planmarks/2FAK/Firmware/Non-Resident CTAP2.0-2.1/targets/stm32l432/src/u2f_compat.h

#ifndef U2F_COMPAT_H
#define U2F_COMPAT_H

// FIXME finish or remove sanity check handling
#define sanity_check_passed     (1)

#define u2f_delay(ms)       delay(ms)
#define data


#endif //U2F_COMPAT_H
