planmarks/2FAK/Firmware/Non-Resident CTAP2.0-2.1/targets/stm32l432/bootloader/bootloader.c

// Copyright 2019 SoloKeys Developers
//
// Licensed under the Apache License, Version 2.0, <LICENSE-APACHE or
// http://apache.org/licenses/LICENSE-2.0> or the MIT license <LICENSE-MIT or
// http://opensource.org/licenses/MIT>, at your option. This file may not be
// copied, modified, or distributed except according to those terms.

#include <stdint.h>
#include <stdlib.h>

#include APP_CONFIG
#include "uECC.h"
#include "u2f.h"
#include "device.h"
#include "flash.h"
#include "crypto.h"
#include "led.h"
#include "memory_layout.h"
#include "ctap_errors.h"
#include "log.h"

volatile version_t current_firmware_version __attribute__ ((section (".flag2"))) __attribute__ ((__used__)) =  {
  .major = SOLO_VERSION_MAJ,
  .minor = SOLO_VERSION_MIN,
  .patch = SOLO_VERSION_PATCH,
  .reserved = 0
};

extern uint8_t REBOOT_FLAG;

typedef enum
{
    BootWrite = 0x40,
    BootDone = 0x41,
    BootCheck = 0x42,
    BootErase = 0x43,
    BootVersion = 0x44,
    BootReboot = 0x45,
    BootBootloader = 0x46,
    BootDisable = 0x47,
    BootPubkey = 0x48,
} BootOperation;


typedef struct {
    uint8_t op;
    uint8_t addr[3];
    uint8_t tag[4];
    uint8_t lenh;
    uint8_t lenl;
    uint8_t payload[255 - 10];
} __attribute__((packed)) BootloaderReq;

uint8_t * last_written_app_address = 0;

/**
 * Erase all application pages. **APPLICATION_END_PAGE excluded**.
 */
static void erase_application()
{
    int page;
    last_written_app_address = (uint8_t*) 0;
    for(page = APPLICATION_START_PAGE; page < APPLICATION_END_PAGE; page++)
    {
        flash_erase_page(page);
    }
}

static void disable_bootloader()
{
    // Clear last 4 bytes of the last application page-1, which is 108th
    uint8_t page[PAGE_SIZE];
    memmove(page, (uint8_t*)LAST_ADDR, PAGE_SIZE);
    memset(page+PAGE_SIZE -4, 0, 4);
    flash_erase_page(LAST_PAGE);
    flash_write(LAST_ADDR, page, PAGE_SIZE);
}

static void authorize_application()
{
    // Do nothing, if is_authorized_to_boot() returns true, otherwise
    // clear first 4 bytes of the last 8 bytes of the page 108.

    // uint32_t zero = 0;
    // uint32_t * ptr;
    // ptr = (uint32_t *)AUTH_WORD_ADDR;
    // flash_write((uint32_t)ptr, (uint8_t *)&zero, 4);
    uint8_t page[PAGE_SIZE];
    if (is_authorized_to_boot())
        return;
    // FIXME refactor: code same as in disable_bootloader(), except clearing start address (-8)
    memmove(page, (uint8_t*)LAST_ADDR, PAGE_SIZE);
    memset(page+PAGE_SIZE -8, 0, 4);
    flash_erase_page(LAST_PAGE);
    flash_write(LAST_ADDR, page, PAGE_SIZE);
}

int is_authorized_to_boot()
{
    // return true, if (uint32_t)AUTH_WORD_ADDR is equal 0
    // Page -4 -> 124
    uint32_t * auth = (uint32_t *)AUTH_WORD_ADDR;
    return *auth == 0;
}

int is_bootloader_disabled()
{
    // return true, if (uint32_t)AUTH_WORD_ADDR+4 is equal 0
    // Page -4 -> 124
    uint32_t * auth = (uint32_t *)(AUTH_WORD_ADDR+4);
    return *auth == 0;
}

#include "version.h"
bool is_firmware_version_newer_or_equal()
{

    if (last_written_app_address == 0) {
        return false;
    }

    printf1(TAG_BOOT,"Current firmware version: %u.%u.%u.%u (%02x.%02x.%02x.%02x)\r\n",
          current_firmware_version.major, current_firmware_version.minor, current_firmware_version.patch, current_firmware_version.reserved,
          current_firmware_version.major, current_firmware_version.minor, current_firmware_version.patch, current_firmware_version.reserved
          );
  volatile version_t * new_version = ((volatile version_t *) (last_written_app_address-8+4));
  printf1(TAG_BOOT,"Uploaded firmware version: %u.%u.%u.%u (%02x.%02x.%02x.%02x)\r\n",
          new_version->major, new_version->minor, new_version->patch, new_version->reserved,
          new_version->major, new_version->minor, new_version->patch, new_version->reserved
          );

  const bool allowed = is_newer((const version_t *)new_version, (const version_t *)&current_firmware_version) || current_firmware_version.raw == 0xFFFFFFFF;
  if (allowed){
    printf1(TAG_BOOT, "Update allowed, setting new firmware version as current.\r\n");
//    current_firmware_version.raw = new_version.raw;
    uint8_t page[PAGE_SIZE];
    memmove(page, (uint8_t*)BOOT_VERSION_ADDR, PAGE_SIZE);
    memmove(page, (version_t*) new_version, 4);
    printf1(TAG_BOOT, "Writing\r\n");
    flash_erase_page(BOOT_VERSION_PAGE);
    flash_write(BOOT_VERSION_ADDR, page, PAGE_SIZE);
    printf1(TAG_BOOT, "Finish\r\n");
  } else {
    printf1(TAG_BOOT, "Firmware older - update not allowed.\r\n");
  }
  return allowed;
}

/**
 * Execute bootloader commands
 * @param klen key length - length of the bootloader request
 * @param keyh key handle - bootloader request, packeted as key handle
 * @return
 */
int bootloader_bridge(int klen, uint8_t * keyh)
{
    static int has_erased = 0;
    BootloaderReq * req =  (BootloaderReq *  )keyh;
#ifndef SOLO_HACKER
    uint8_t hash[32];
#endif
    uint8_t version = 1;
    uint16_t len = (req->lenh << 8) | (req->lenl);

    if (len > klen-10)
    {
        printf1(TAG_BOOT,"Invalid length %d / %d\r\n", len, klen-9);
        return CTAP1_ERR_INVALID_LENGTH;
    }
#ifndef SOLO_HACKER
    extern uint8_t pubkey_boot[];
    extern const uint8_t pubkey_boot_size;
    const struct uECC_Curve_t * curve = NULL;
#endif

    // Translate and enclose the requested address in the MCU flash space, starting from 0x8000000
    uint32_t addr = ((*((uint32_t*)req->addr)) & 0xffffff) | 0x8000000;

    uint32_t * ptr = (uint32_t *)addr;
    uint32_t current_address;

    switch(req->op){
        case BootWrite:
            // Write to MCU's flash.
            printf1(TAG_BOOT, "BootWrite: %08lx\r\n",(uint32_t)ptr);
            // Validate write range.
            if (   (uint32_t)ptr < APPLICATION_START_ADDR
                || (uint32_t)ptr >= APPLICATION_END_ADDR
                || ((uint32_t)ptr+len) > APPLICATION_END_ADDR)
            {
                printf1(TAG_BOOT,"Bound exceeded [%08lx, %08lx]\r\n",APPLICATION_START_ADDR,APPLICATION_END_ADDR);
                return CTAP2_ERR_NOT_ALLOWED;
            }

            // Clear all application pages, if not done already.
            if (!has_erased || is_authorized_to_boot())
            {
                erase_application();
                has_erased = 1;
            }
            // Fail, if the validation procedure passes.
            if (is_authorized_to_boot())
            {
                printf2(TAG_ERR, "Error, boot check bypassed\n");
                exit(1);
            }
            current_address = addr + len;
            if (current_address < (uint32_t) last_written_app_address) {
                printf2(TAG_ERR, "Error, only ascending writes allowed.\n");
                has_erased = 0;
                return CTAP2_ERR_NOT_ALLOWED;
            }
            last_written_app_address = (uint8_t*) current_address;

            // Do the actual write
            flash_write((uint32_t)ptr,req->payload, len);
            break;
        case BootDone:
            // Writing to flash finished. Request code validation.
            printf1(TAG_BOOT, "BootDone: \r\n");
#ifndef SOLO_HACKER
#pragma message ("Verifying bootloader enabled")
            if (len != 64)
            {
                printf1(TAG_BOOT,"Invalid length for signature\r\n");
                return CTAP1_ERR_INVALID_LENGTH;
            }
            dump_hex1(TAG_BOOT, req->payload, 32);
            // Hash all code, included in the application pages, SHA256
            ptr = (uint32_t *)APPLICATION_START_ADDR;
            crypto_sha256_init();
            crypto_sha256_update((uint8_t*)ptr, APPLICATION_END_ADDR-APPLICATION_START_ADDR);
            crypto_sha256_final(hash);
            curve = uECC_secp256r1();
            // Verify incoming signature made over the SHA256 hash
            if (
                    !uECC_verify(pubkey_boot, hash, 32, req->payload, curve)
            )
            {
                printf1(TAG_BOOT, "Signature invalid\r\n");
                dump_arrl(TAG_BOOT, pubkey_boot, pubkey_boot_size);
                dump_arrl(TAG_BOOT, hash, 32);
                REBOOT_FLAG = 1;
                return CTAP2_ERR_OPERATION_DENIED;
            }
            printf1(TAG_BOOT, "Signature valid\r\n");
            if (!is_firmware_version_newer_or_equal()){
              printf1(TAG_BOOT, "Firmware older - update not allowed.\r\n");
              printf1(TAG_BOOT, "Rebooting...\r\n");
              REBOOT_FLAG = 1;
              return CTAP2_ERR_OPERATION_DENIED;
            }
#endif
            // Set the application validated, and mark for reboot.
            authorize_application();

            REBOOT_FLAG = 1;
            break;
        case BootCheck:
            return 0;
            break;
        case BootErase:
            printf1(TAG_BOOT, "BootErase.\r\n");
            erase_application();
            return 0;
            break;
#ifndef SOLO_HACKER
        case BootPubkey:
            has_erased = 0;
            printf1(TAG_BOOT, "BootPubkey.\r\n");
#define MIN(x, y) (((x) < (y)) ? (x) : (y))
            u2f_response_writeback(pubkey_boot, MIN(pubkey_boot_size, 71) );
            break;
#undef MIN
#endif
        case BootVersion:
            has_erased = 0;
            printf1(TAG_BOOT, "BootVersion.\r\n");
            version = SOLO_VERSION_MAJ;
            u2f_response_writeback(&version,1);
            version = SOLO_VERSION_MIN;
            u2f_response_writeback(&version,1);
            version = SOLO_VERSION_PATCH;
            u2f_response_writeback(&version,1);

            version = 0xFF;
            u2f_response_writeback(&version,1);
            u2f_response_writeback((uint8_t*) USBD_PRODUCT_FS_STRING, strlen(USBD_PRODUCT_FS_STRING));
            u2f_response_writeback(&version,1);
            u2f_response_writeback((uint8_t*) USBD_MANUFACTURER_STRING, strlen(USBD_MANUFACTURER_STRING));
            u2f_response_writeback(&version,1);
            break;
        case BootReboot:
            printf1(TAG_BOOT, "BootReboot.\r\n");
            printf1(TAG_BOOT, "Application authorized: %d.\r\n", is_authorized_to_boot());
            REBOOT_FLAG = 1;
            break;
        case BootDisable:
            // Disable bootloader using a magic bytes as a confirmation phrase.
            printf1(TAG_BOOT, "BootDisable %08lx.\r\n", *(uint32_t *)(AUTH_WORD_ADDR+4));
            if (req->payload[0] == 0xcd && req->payload[1] == 0xde
               && req->payload[2] == 0xba && req->payload[3] == 0xaa)
            {
                disable_bootloader();
                version = 0;
                u2f_response_writeback(&version,1);
            }
            else
            {
                version = CTAP2_ERR_OPERATION_DENIED;
                u2f_response_writeback(&version,1);
            }
            break;
#ifdef SOLO_HACKER
        case BootBootloader:
            // Boot ST bootloader
            printf1(TAG_BOOT, "BootBootloader.\r\n");
            flash_option_bytes_init(1);
            boot_st_bootloader();
            break;
#endif
        default:
            return CTAP1_ERR_INVALID_COMMAND;
    }
    return 0;
}

/**
 * Control LEDs while in the bootloader.
 */
void bootloader_heartbeat()
{
#ifdef BOOTLOADER_HEARTBEAT
    static int state = 0;
    static uint32_t val = (LED_MAX_SCALER - LED_MIN_SCALER)/2;
    uint8_t r = (LED_INIT_VALUE >> 16) & 0xff;
    uint8_t g = (LED_INIT_VALUE >> 8) & 0xff;
    uint8_t b = (LED_INIT_VALUE >> 0) & 0xff;

    if (state)
    {
        val--;
    }
    else
    {
        val++;
    }

    if (val > LED_MAX_SCALER || val < LED_MIN_SCALER)
    {
        state = !state;
    }

    led_rgb(((val * g)<<8) | ((val*r) << 16) | (val*b));
#endif
}

uint32_t ctap_atomic_count(uint32_t amount)
{
    static uint32_t count = 1000;
    count += (amount + 1);
    return count;
}
